Norman-w/HiLink-RM65-Router/docs/extracted/kit/HLK-AX3000-KIT-原理图.pdf

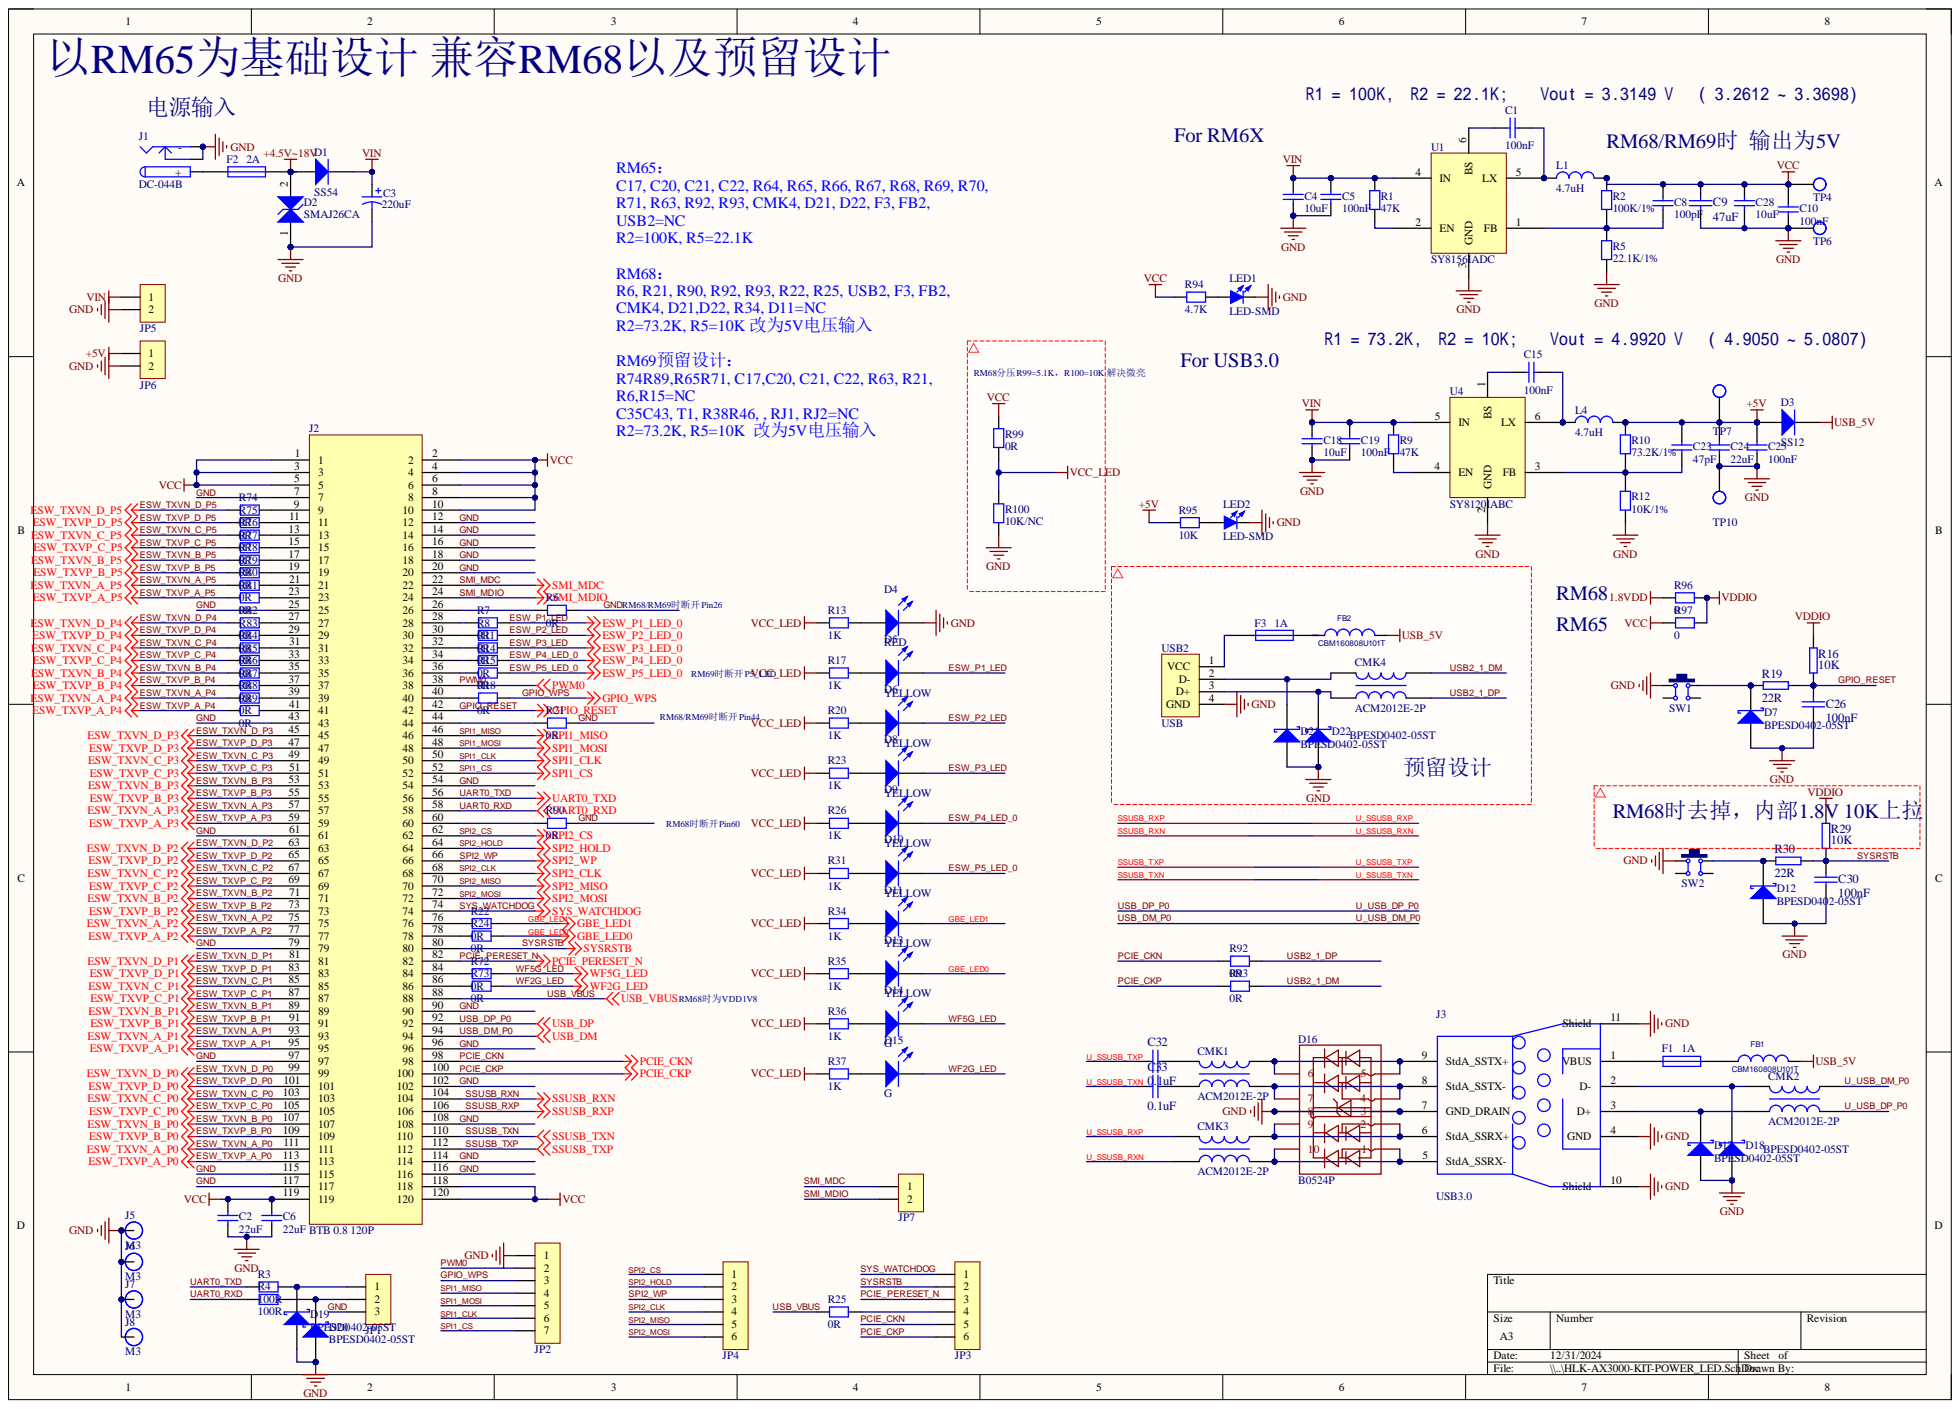
[picture p20: page 1]

0RR75 | 1 | G N D
0RR76 | | G N D
0RR77 | | G N D

Si z e A 3 | Numbe r

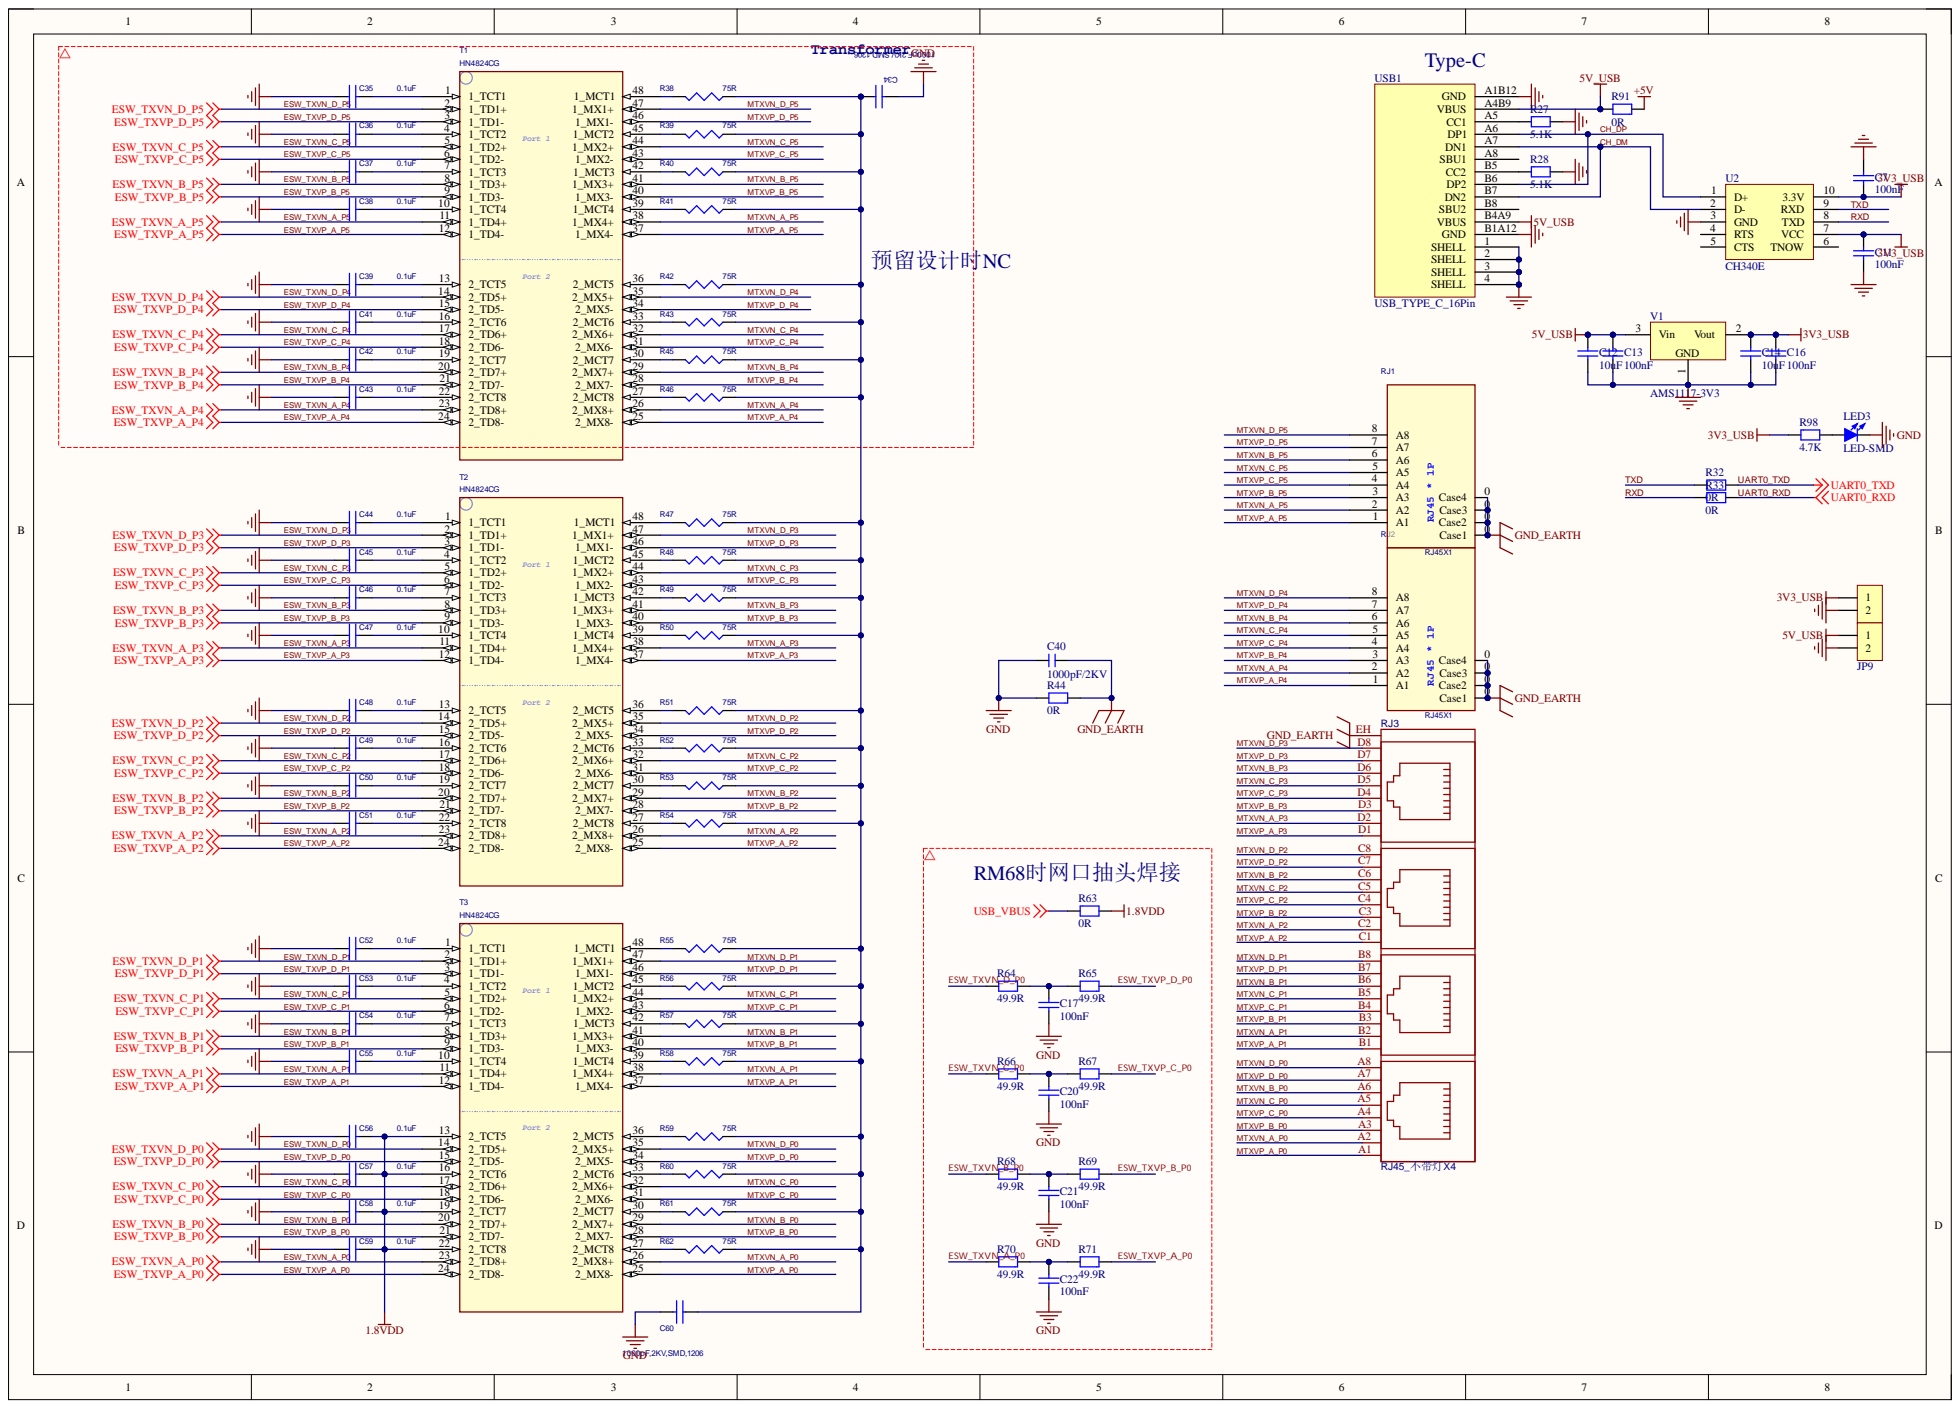
[picture p21: page 2]
